Laptopmini/PorschePi/beocreate/docs/connectors.png

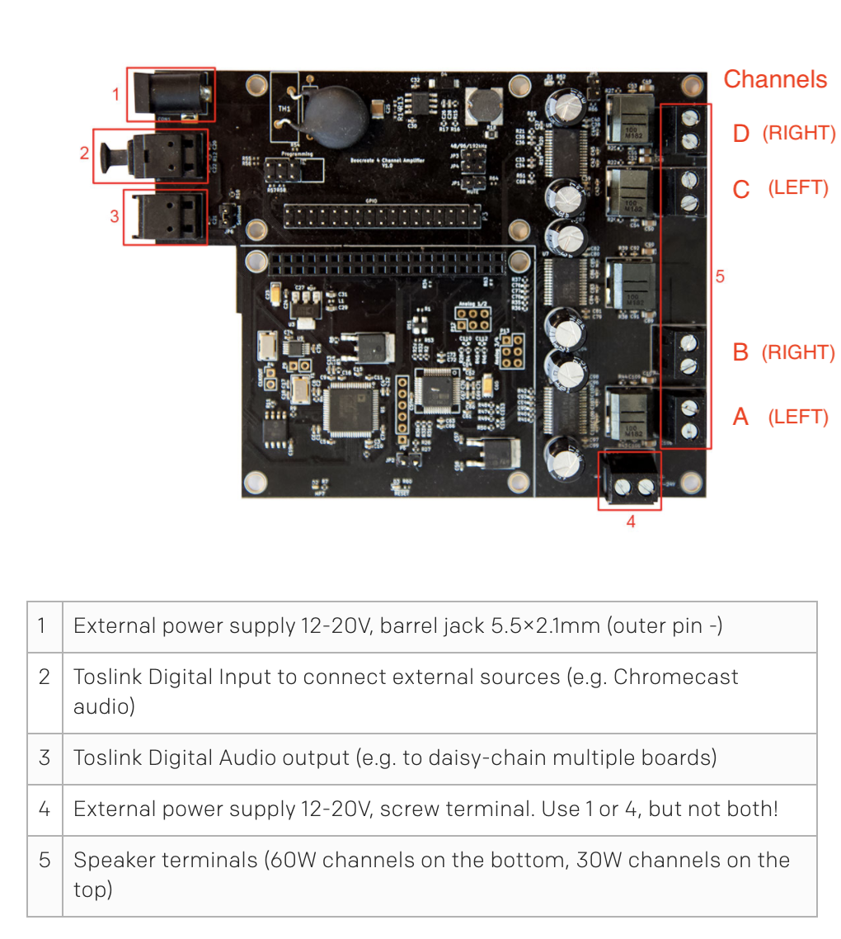
beocreate/docs/connectors.png
