Laptopmini/PorschePi/beocreate/docs/reserved-gpio.png

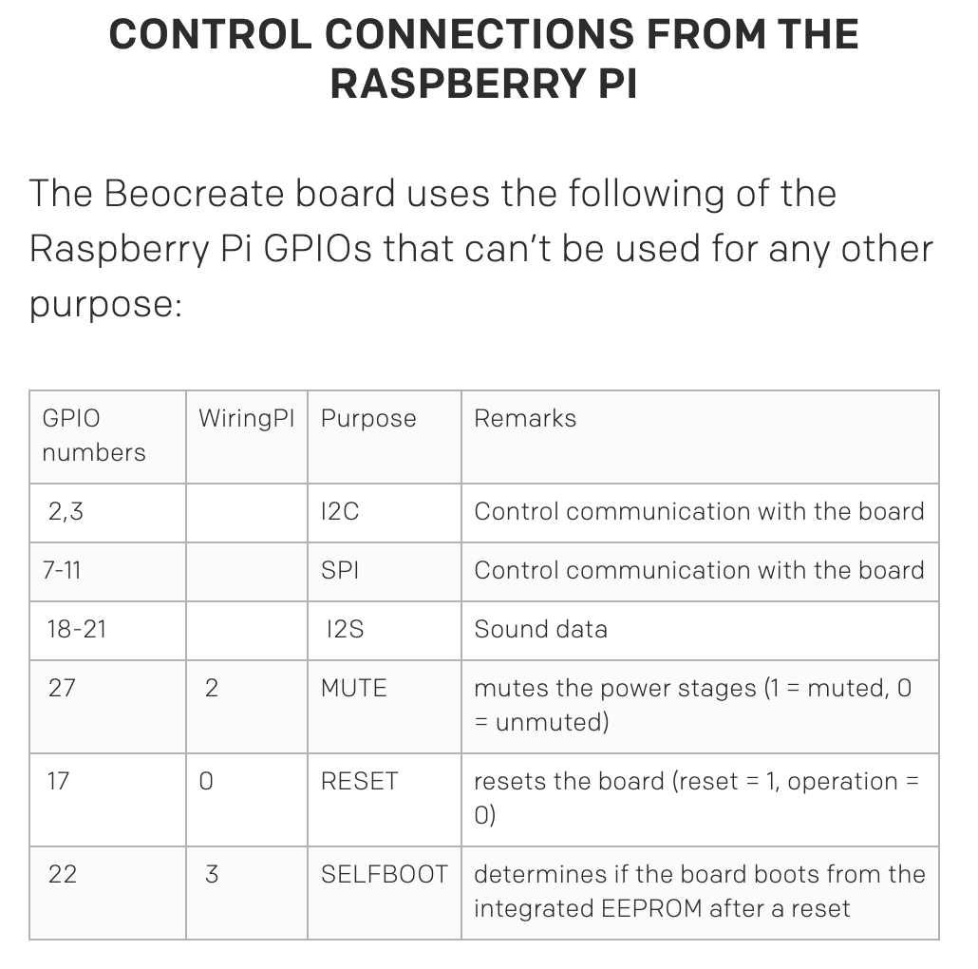
beocreate/docs/reserved-gpio.png
